ageppert/SAO_Etch_sAo_Sketch/Datasheets/OLED 1.5 128x128 drawing 2.png

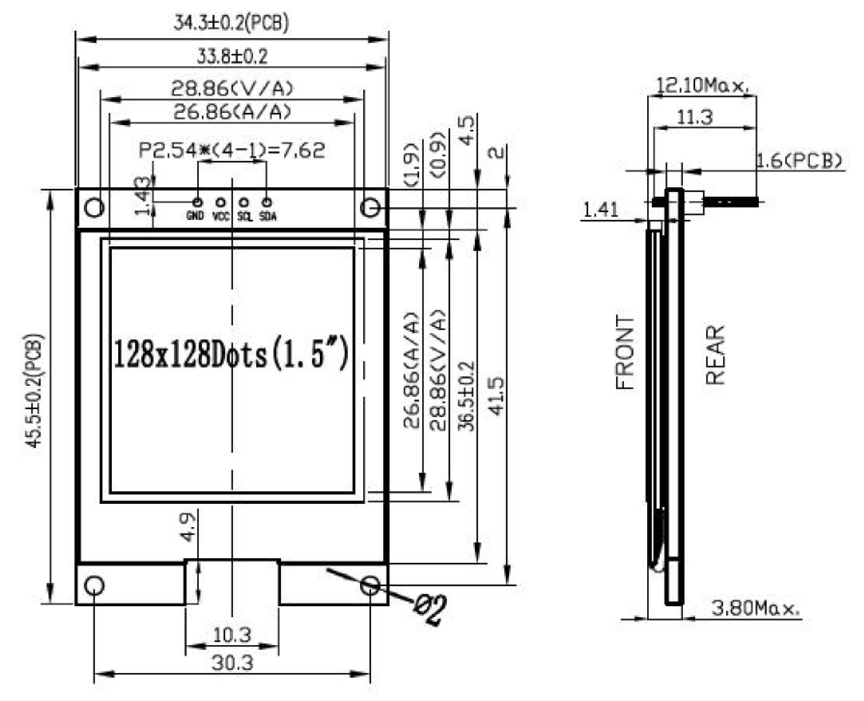
Datasheets/OLED 1.5 128x128 drawing 2.png
