ageppert/SAO_Etch_sAo_Sketch/Datasheets/OLED 1.5 GME128128-02 V3.1 with notch.png

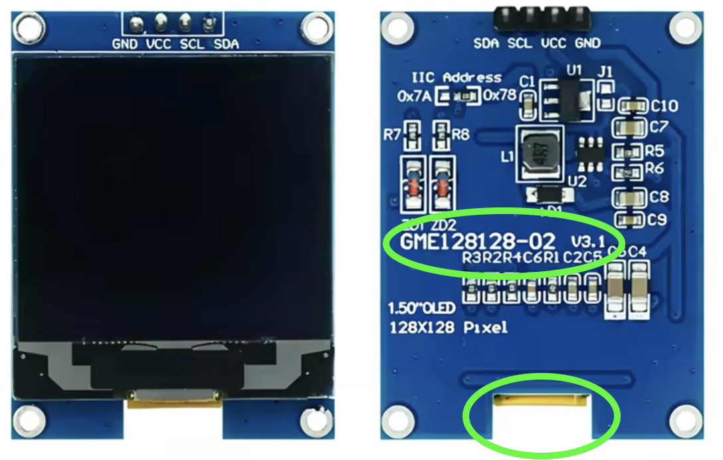
Datasheets/OLED 1.5 GME128128-02 V3.1 with notch.png
