ageppert/SAO_Etch_sAo_Sketch/Images/Etch_sAo_Sketch V1 Render Bottom.png

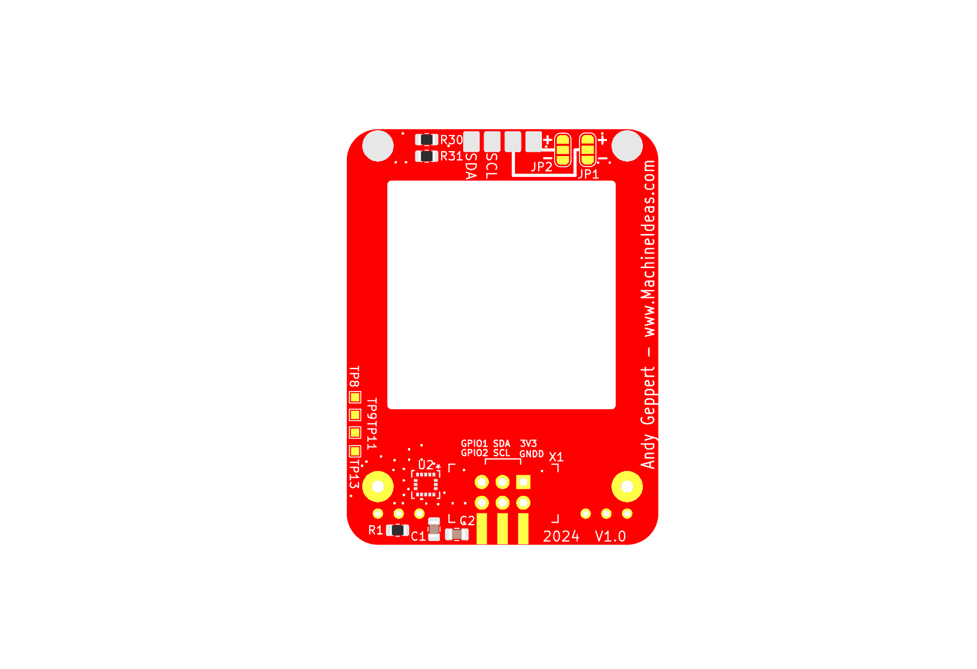
Images/Etch_sAo_Sketch V1 Render Bottom.png
