ageppert/SAO_Etch_sAo_Sketch/Images/GooDisplay 1.54.png

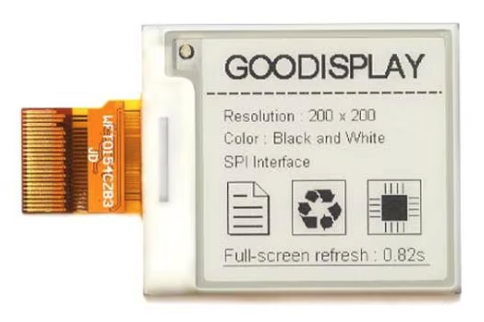
Images/GooDisplay 1.54.png
