ageppert/SAO_Etch_sAo_Sketch/Images/RIGHT OLED 128x128 V3 back side.jpg

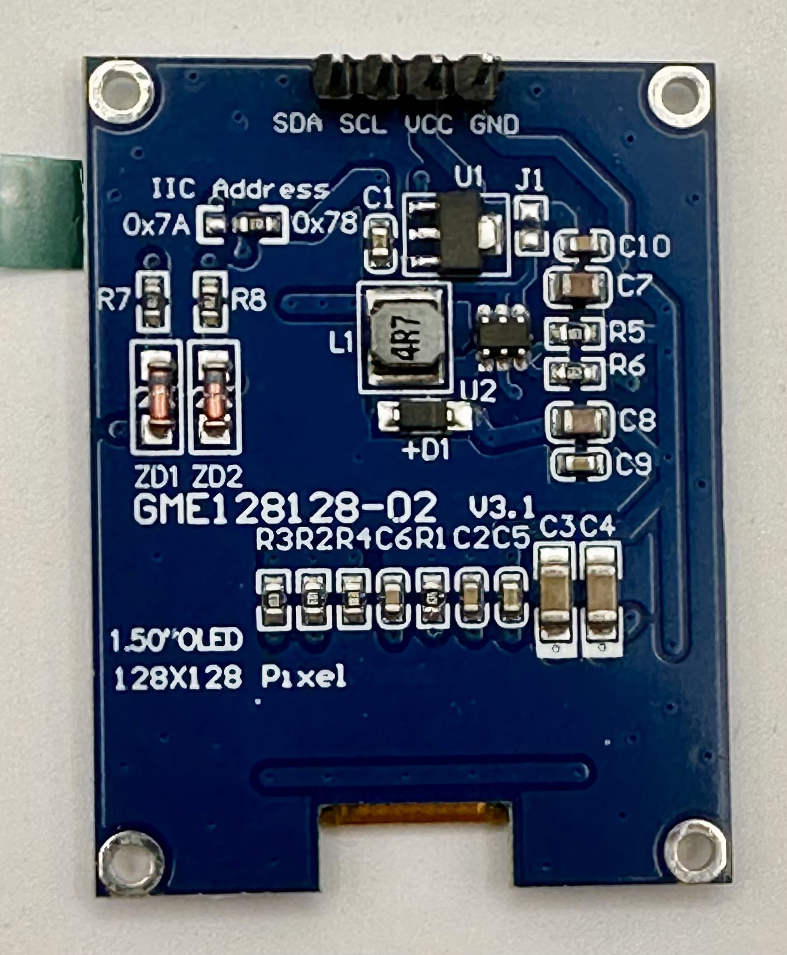
Images/RIGHT OLED 128x128 V3 back side.jpg
