ageppert/SAO_Etch_sAo_Sketch/Images/SAO Sketch Render Back V1.2.png

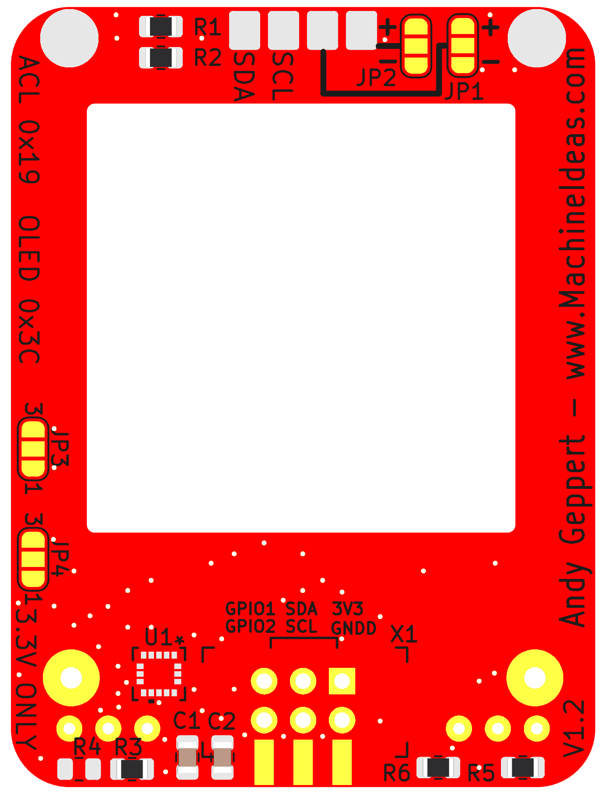
Images/SAO Sketch Render Back V1.2.png
