ageppert/SAO_Etch_sAo_Sketch/Images/SAO Sketch Render Front V1.3.png

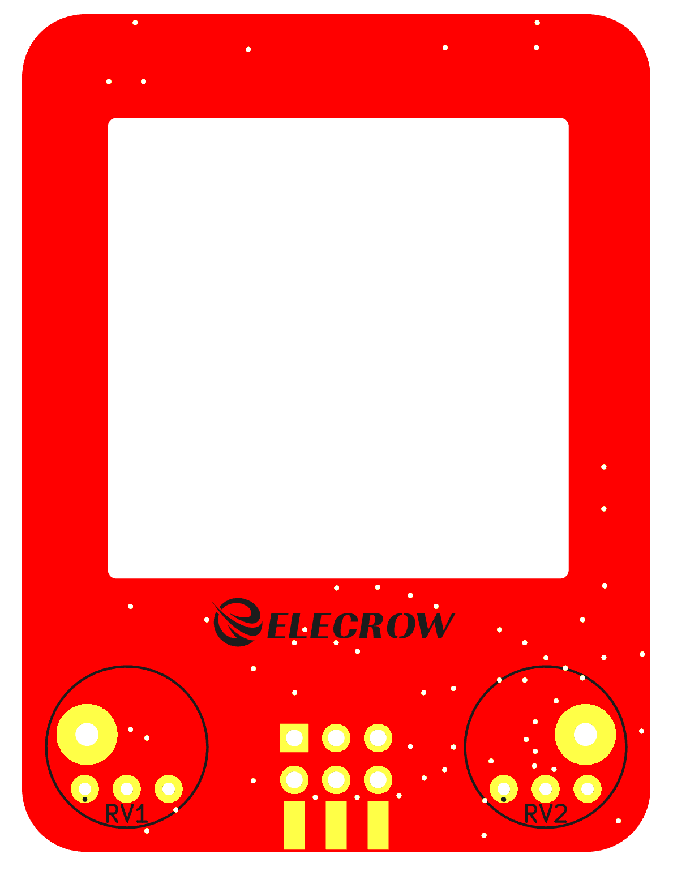
Images/SAO Sketch Render Front V1.3.png
