ageppert/SAO_Etch_sAo_Sketch/Images/Wrong OLED 128x128 V2.0 Advanced Tech.jpg

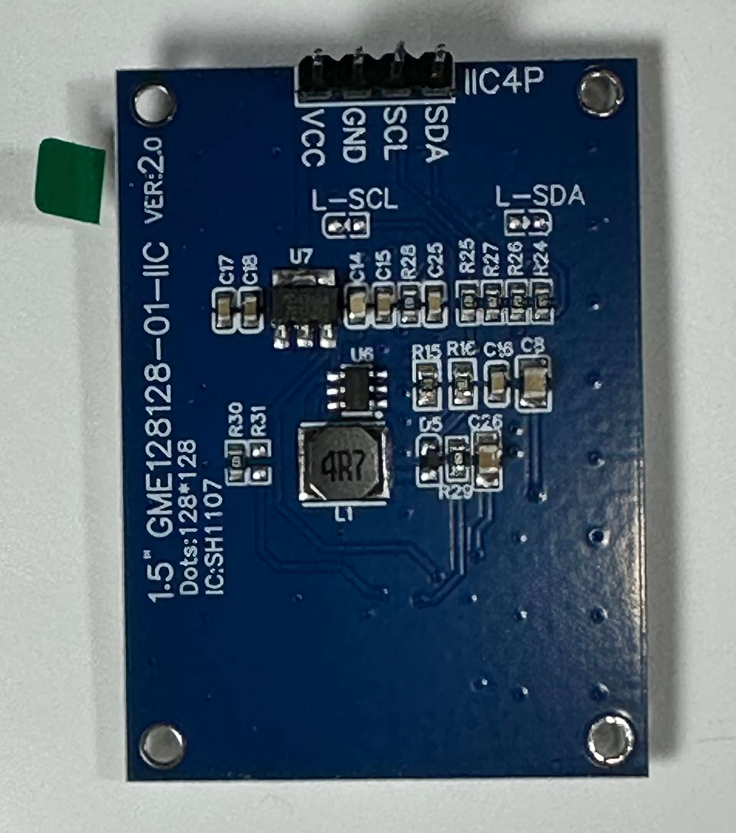
Images/Wrong OLED 128x128 V2.0 Advanced Tech.jpg
