ageppert/SAO_Etch_sAo_Sketch/Firmware/Supercon.8_Badge_Micropython/ssd1327.py

"""
MicroPython SSD1327 OLED I2C driver
https://github.com/mcauser/micropython-ssd1327

MIT License
Copyright (c) 2017 Mike Causer

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
__version__ = '1.1.1'

from micropython import const
import framebuf

# commands
SET_COL_ADDR          = const(0x15)
SET_SCROLL_DEACTIVATE = const(0x2E)
SET_ROW_ADDR          = const(0x75)
SET_CONTRAST          = const(0x81)
SET_SEG_REMAP         = const(0xA0)
SET_DISP_START_LINE   = const(0xA1)
SET_DISP_OFFSET       = const(0xA2)
SET_DISP_MODE         = const(0xA4) # 0xA4 normal, 0xA5 all on, 0xA6 all off, 0xA7 when inverted
SET_MUX_RATIO         = const(0xA8)
SET_FN_SELECT_A       = const(0xAB)
SET_DISP              = const(0xAE) # 0xAE power off, 0xAF power on
SET_PHASE_LEN         = const(0xB1)
SET_DISP_CLK_DIV      = const(0xB3)
SET_SECOND_PRECHARGE  = const(0xB6)
SET_GRAYSCALE_TABLE   = const(0xB8)
SET_GRAYSCALE_LINEAR  = const(0xB9)
SET_PRECHARGE         = const(0xBC)
SET_VCOM_DESEL        = const(0xBE)
SET_FN_SELECT_B       = const(0xD5)
SET_COMMAND_LOCK      = const(0xFD)

# registers
REG_CMD  = const(0x80)
REG_DATA = const(0x40)

class SSD1327:
    def __init__(self, width=128, height=128):
        self.width = width
        self.height = height
        self.buffer = bytearray(self.width * self.height // 2)
        self.framebuf = framebuf.FrameBuffer(self.buffer, self.width, self.height, framebuf.GS4_HMSB)

        self.col_addr = ((128 - self.width) // 4, 63 - ((128 - self.width) // 4))
        # 96x96     (8, 55)
        # 128x128   (0, 63)

        self.row_addr = (0, self.height - 1)
        # 96x96     (0, 95)
        # 128x128   (0, 127)

        self.offset = 128 - self.height
        # 96x96     32
        # 128x128   0

        self.poweron()
        self.init_display()

    def init_display(self):
        for cmd in (
            SET_COMMAND_LOCK, 0x12, # Unlock
            SET_DISP, # Display off
            # Resolution and layout
            SET_DISP_START_LINE, 0x00,
            SET_DISP_OFFSET, self.offset, # Set vertical offset by COM from 0~127
            # Set re-map
            # Enable column address re-map
            # Disable nibble re-map
            # Horizontal address increment
            # Enable COM re-map
            # Enable COM split odd even
            SET_SEG_REMAP, 0x51,
            SET_MUX_RATIO, self.height - 1,
            # Timing and driving scheme
            SET_FN_SELECT_A, 0x01, # Enable internal VDD regulator
            SET_PHASE_LEN, 0x51, # Phase 1: 1 DCLK, Phase 2: 5 DCLKs
            SET_DISP_CLK_DIV, 0x01, # Divide ratio: 1, Oscillator Frequency: 0
            SET_PRECHARGE, 0x08, # Set pre-charge voltage level: VCOMH
            SET_VCOM_DESEL, 0x07, # Set VCOMH COM deselect voltage level: 0.86*Vcc
            SET_SECOND_PRECHARGE, 0x01, # Second Pre-charge period: 1 DCLK
            SET_FN_SELECT_B, 0x62, # Enable enternal VSL, Enable second precharge
            # Display
            SET_GRAYSCALE_LINEAR, # Use linear greyscale lookup table
            SET_CONTRAST, 0x7f, # Medium brightness
            SET_DISP_MODE, # Normal, not inverted
            SET_COL_ADDR, self.col_addr[0], self.col_addr[1],
            SET_ROW_ADDR, self.row_addr[0], self.row_addr[1],
            SET_SCROLL_DEACTIVATE,
            SET_DISP | 0x01): # Display on
            self.write_cmd(cmd)
        self.fill(0)
        self.write_data(self.buffer)

    def poweroff(self):
        self.write_cmd(SET_FN_SELECT_A)
        self.write_cmd(0x00) # Disable internal VDD regulator, to save power
        self.write_cmd(SET_DISP)

    def poweron(self):
        self.write_cmd(SET_FN_SELECT_A)
        self.write_cmd(0x01) # Enable internal VDD regulator
        self.write_cmd(SET_DISP | 0x01)

    def contrast(self, contrast):
        self.write_cmd(SET_CONTRAST)
        self.write_cmd(contrast) # 0-255

    def rotate(self, rotate):
        self.poweroff()
        self.write_cmd(SET_DISP_OFFSET)
        self.write_cmd(self.height if rotate else self.offset)
        self.write_cmd(SET_SEG_REMAP)
        self.write_cmd(0x42 if rotate else 0x51)
        self.poweron()

    def invert(self, invert):
        self.write_cmd(SET_DISP_MODE | (invert & 1) << 1 | (invert & 1)) # 0xA4=Normal, 0xA7=Inverted

    def show(self):
        self.write_cmd(SET_COL_ADDR)
        self.write_cmd(self.col_addr[0])
        self.write_cmd(self.col_addr[1])
        self.write_cmd(SET_ROW_ADDR)
        self.write_cmd(self.row_addr[0])
        self.write_cmd(self.row_addr[1])
        self.write_data(self.buffer)

    def fill(self, col):
        self.framebuf.fill(col)

    def pixel(self, x, y, col):
        self.framebuf.pixel(x, y, col)

    def line(self, x1, y1, x2, y2, col):
        self.framebuf.line(x1, y1, x2, y2, col)

    def scroll(self, dx, dy):
        self.framebuf.scroll(dx, dy)
        # software scroll
        
    def text(self, string, x, y, col=15):
        self.framebuf.text(string, x, y, col)

    def write_cmd(self):
        raise NotImplementedError

    def write_data(self):
        raise NotImplementedError


class SSD1327_I2C(SSD1327):
    def __init__(self, width, height, i2c, addr=0x3c):
        self.i2c = i2c
        self.addr = addr
        self.cmd_arr = bytearray([REG_CMD, 0])  # Co=1, D/C#=0
        self.data_list = [bytes((REG_DATA,)), None]
        super().__init__(width, height)

    def write_cmd(self, cmd):
        self.cmd_arr[1] = cmd
        self.i2c.writeto(self.addr, self.cmd_arr)

    def write_data(self, data_buf):
        segments = self.split_into_segments(data_buf)
        for i, segment in enumerate(segments):
            self.data_list[1] = segment
            self.i2c.writevto(self.addr, self.data_list)

    def split_into_segments(self, ydata, segment_length=1024):
        """Split an array into segments, so we don't timeout"""
        return [ydata[i : i + segment_length] for i in range(0, len(ydata), segment_length)]


class WS_OLED_128X128(SSD1327_I2C):
    def __init__(self, i2c, addr=0x3c):
        super().__init__(128, 128, i2c, addr)
        
# Example usage
if __name__ == "__main__":
    from machine import Pin, SoftI2C
    # Initialize I2C
    i2c = SoftI2C(sda=Pin(26), scl=Pin(27))
    
    display = WS_OLED_128X128(i2c)

    display.fill(0)
    for x in range(0,127):
        for y in range(0,127):
            display.pixel(x,y,15)
            display.show()
    display.show()
