ageppert/SAO_Etch_sAo_Sketch/Firmware/Etch_sAo_Sketch_RP2040_Demo/Etch_sAo_Sketch_RP2040_Demo.ino

/******************************************************************************************************************
  Etch sAo Sketch (EAS) Demo code using RP2040 and the Arduino IDE

  Github repo: https://github.com/ageppert/SAO_Etch_sAo_Sketch
  Project page: https://hackaday.io/project/197581-etch-sao-sketch

  DEPENDENCIES - FIRMWARE
    This demo will work with a huge range of IDEs and hardware, but it was developed and tested with the following:
    Arduino IDE 2.3.2
      Install "Arduino Mbed OS RP2040 Boards" v4.2.2 with Arduino Boards Manager
        - The Wire Library is included.
      Adafruit SSD1327 libray with dependencies:
        - Adafruit BusIO
        - Adafruit GFX Library
      Adafruit LIS3DH libray with dependencies:
        - Adafruit BusIO
        - Adafruit Unified Sensor

  DEPENDENCIES - HARDWARE
    OLED with SSD1327 Driver
    Accelerometer LIS3DH
    External user provided RP2040 MCU tested so far

  CONFIGURE SAO DEMO CONTROLLER FOR ETCH SAO SKETCH HARDWARE V1.0
    If you are using SAO Demo Controller V2 with EAS V1.0 you need to close solder jumper JP5&6 pads 2-3 so the
    analog pots will be connected to GP26/ADC0 and GP27/ADC1 of the RP2040-Zero on the SAO Demo Controller. This enables
    access to the full range of the potentiometers in EAS V1.0 which are configured for 0 to 3.3V ADC sensing.
    Etch sAo Sketch V1.1+ can access full range pot control with the ADC in the accelerometer.

  CONFIGURE THIS FIRMWARE TO WORK WITH CORRECT ETCH SAO SKETCH HARDWARE
    See the ETCH SAO SKETCH - HARDWARE VERSION TABLE and hardware version setting variables immediately below it to compile
    this firmware to work correctly with your specific Etch sAo Sketch board.

  HARDWARE CONNECTIONS
    OLED 1.5" 128x128 SSD1327: https://learn.adafruit.com/adafruit-grayscale-1-5-128x128-oled-display/arduino-wiring-and-test
    Accelerometer LIS3DH: https://learn.sparkfun.com/tutorials/lis3dh-hookup-guide and https://learn.adafruit.com/adafruit-lis3dh-triple-axis-accelerometer-breakout/arduino  
    Demo board -> RP2040-Zero (miniature Pico/RP2040 dev board) https://www.waveshare.com/rp2040-zero.htm
    The SAO port (X1) is intended to provide full access to the accelerometer, screen, and analog pots.
    SAO I2C pins connect to the OLED and Accelerometer (which also has the potentionmeters connected to built-in ADCs).
    SAO GPIO1 pin connected to the left Analog Potentiometer
    SAO GPIO2 pin connected to the right Analog Potentiometer
  
  MODES OF OPERATION
    MODE_INIT
      Connect to the serial port for status and debugging  
    MODE_BOOT_SCREEN
      Startup with the boot screen. Configured analog input source per hardware version specified beloe the HARDWARE VERSION TABLE.
      After timeout, automatcally go to sketching mode with default black background.
    MODE_SKETCH
      In sketch mode, rotate pots to draw.
      Gestures active during sketch mode:
        Upsidedown, shake left/right to clear sketch zone.
        Rightsideup, shake left/right to change background color (also clears screen).
        Rightsideup, shake up/down to change pot input between Arduino Analog port (0-3.3V) or accelerometer analog ports (0.8-1.6V).
    MODE_AT_THE_END_OF_TIME
      I hope you never land in this mode!

  /************************************ ETCH SAO SKETCH - FWV (FIRMWARE VERSION) TABLE ******************************
  | VERSION |  DATE      | MCU     | DESCRIPTION                                                                    |
  -------------------------------------------------------------------------------------------------------------------
  |  1.0.0  | 2024-11-01 | RP2040  | First draft, hurry up for Supercon!
  |  1.1.0  | 2024-11-23 | RP2040  | Correct pot scaling for full range hardware mods with Accel ADC.
  |  1.3.0  | 2025-04-12 | RP2040  | Clarify hardware versions and configurations. Supports all hardware versions.
  |  1.3.1  | 2025-04-18 | RP2040  | Fix and improve shake side-to-side (upside down or right side up) to erase,
  |         |            |         |   disable screen inversion and pot input select gestures. Add LOAD and RUN, 
  |         |            |         |   and display firmware/hardware versions.
  |  1.3.2  | 2025-04-25 | RP2040  | Fix glitching wrap-around at ends by bounding ADC count reading with HWV1.3.
  |  1.3.3  | 2025-04-25 | RP2040  | Tighten ADC left/bottom range to ensure drawing to edges of screen with HWV1.1+.
  |  1.3.4  | 2025-08-16 | RP2040  | Quicker boot up, red LED breathing.
  |  1.3.5  | 2025-08-16 | RP2040  | Adjusted low end voltage/ADC to work with 3.0V supply, accounting for Demo Controller V2 diode drop.
  |  1.3.6  | 2025-09-26 | RP2040  | Add support to optionally connect Etch sAo Sketch to the incoming SAO port I2C1 to fully cover the Demo Controller.
  |  1.3.7  | 2026-09-05 | RP2040  | Add calibrate mode via GP14 Button (Demo Controller V2 button, and V3,V4 upper left USER BUTTON 1)
  |         |            |         |   Increase shake-to-clear sensitivity and enable up-down detection for clearing.
  |         |            |         |   Extend default Accelerometer ADC range to fit display better.
  |  1.4.0  | 2026-09-23 | RP2040  | Calibrate pot scaling for hardware version 1.4.0
  |         |            |         | 
  |         |            |         | 
  -----------------------------------------------------------------------------------------------------------------*/
  // TODO: Make this work with Hackaday Supercon 2024 and Berlin 2025 Badge I2C ports 4-5-6 on pins 31 CL / 32 DA GPIO 26/27. 
  //        Ports 1-2-3 on pins 1 DA and 2 CL. GPIO 0/1
    static uint8_t FirmwareVersionMajor  = 1;
    static uint8_t FirmwareVersionMinor  = 4;
    static uint8_t FirmwareVersionPatch  = 0;

  /************************************ ETCH SAO SKETCH - HWV (HARDWARE VERSION) TABLE ******************************
  | VERSION |  DATE      | ADC ?   | DESCRIPTION                                                                    |
  -------------------------------------------------------------------------------------------------------------------
  |  1.0.0  | 2024-09-27 | RP2040  | First prototype, as built, getting it to come alive. Analog input range of pots
  |         |            |  only   |   is much wider than accelerometer analog inputs can handle. Recommend to use
  |         |            |         |   only with 3.3V capable analog inputs of host MCU through SAO port GPIO1&2.
  |  1.0.1  | 2025-04-14 |         | First prototype, without excess pull-up resistors R30 and R31 10K.
  -------------------------------------------------------------------------------------------------------------------
  |  1.1.0  | 2024-11-23 | Accel   | V1.0.0 modified with resistors inline (10K highside and 4.8K lowside) with the
  |         |            |   or    |   pots to enable full travel to map to accelerometer ADC 0.8 to 1.6V input range.
  |  1.1.1  | 2025-04-25 | RP2040  | V1.1.0 with excess pull-up resistors R1/2 removed.
  -------------------------------------------------------------------------------------------------------------------
  |  1.2.0  | 2024-12-10 |         | RFQ only. Same as V1.1.0. Never produced.
  -------------------------------------------------------------------------------------------------------------------
  |  1.3.0  | 2025-01-13 | Accel   | Batch for Hackaday Europe with supplier name Elecrow on the front. Some may be
  |         |            |   or    |   updated with an additional clear Etch sAo Sketch sticker on the top as well.
  |  1.3.1  | 2025-04-13 | RP2040  | Removed R1 and R2 to reduce the excessive pull-up resistance for wider MCU
  |         |            |         |   compatibility (from the red board) and better I2C performance.
  |  1.3.2  | 2026-08-01 |         | Removed resistors R2 and R3 pull-ups and ZD1 and ZD2 diodes from the blue OLED
  |         |            |         |   Board for better I2C performance.
  -------------------------------------------------------------------------------------------------------------------
  |  1.4.0  | 2026-09-23 |         | Gold ENIG Etch sAo Sketch on top. Remove pull-up resistors on main board and 
  |         |            |         |   and OLED board. Remove OLED power solder jumpers.
  |         |            |         |
  -------------------------------------------------------------------------------------------------------------------
  ************************************* ETCH SAO SKETCH - HWV (HARDWARE VERSION) SETTING ****************************
  This will be the default mode of input from the analog pots (I2C Accelerometer ADC = 0 or Arduino/RP2040 ADCs = 1) 
  will be set during MODE_BOOT_SCREEN...                                                                           */
    static bool    EASAnalogSource;
  // ...based on the hardware version set in the following three lines.
    #define HARDWARE_VERSION_MAJOR  1
    #define HARDWARE_VERSION_MINOR  4
    #define HARDWARE_VERSION_PATCH  0
    static uint8_t HardwareVersionMajor  = HARDWARE_VERSION_MAJOR;
    static uint8_t HardwareVersionMinor  = HARDWARE_VERSION_MINOR;
    static uint8_t HardwareVersionPatch  = HARDWARE_VERSION_PATCH;
/*******************************************************************************************************************/

#include <Adafruit_SSD1327.h>
#include <Fonts/FreeMono9pt7b.h>  // https://learn.adafruit.com/adafruit-gfx-graphics-library/using-fonts
#include <Wire.h>                             // RP2040 Pico-Zero default I2C port is GPIO4 (SDA0) and GPIO5 (SCL0).
                                              // RP2040 Pico W default I2C port is GPIO4 (SDA0) and GPIO5 (SCL0).
#include <Adafruit_LIS3DH.h>
#include <Adafruit_Sensor.h>

/****** IMPORTANT ******
  Using the SAO Demo Controller's bottom SAO port with I2C1 means power will enter the system through the USB C port
  on the RP2040-zero. That power is regulated to 3.3V on the RP20240-Zero and must be routed to the I2C1 port. This requires:
    1) soldering on a small wire to the SAO Demo Controller from JP4 pin 1 to JP1 bottom pad 
    2) and removing D1.
  Of course, the SAO socket on the Demo Controller needs to be moved or installed on the top side of the board to accept the 
  Etch sAo Sketch on the top. For more details and illustrations, see the project page linked at the top of this file.
************************/
// Choose only one port by setting one of the following to true:
  // Default top SAO output port I2C0 channel
    #define I2C_PORT0 true
  // Optional use of the bottom SAO "input" port I2C1 channel as an output so Etch sAo Sketch and Demo Controller stack perfectly.
    #define I2C_PORT1 false

// Choose only one filter type
  #define EMA_FILTER     // Uses double precision floating point, slower compute
  // #define IIR_FILTER        // Uses integers, faster

// Filter strength 0 to 1, smaller numbers = heavier filtering
  #define EMA_FILTER_ALPHA_X 0.1
  #define EMA_FILTER_ALPHA_Y 0.1
  #define IIR_FILTER_ALPHA_X 0.05
  #define IIR_FILTER_ALPHA_Y 0.05

#define EAS_V1_4 true

#if I2C_PORT0
  #define I2C0_SDA_PIN 4
  #define I2C0_SCL_PIN 5
#endif

#if I2C_PORT1
  #define I2C1_SDA_PIN 2
  #define I2C1_SCL_PIN 3
#endif

#define UserButtonPin1 14
#define UserButtonPin2 15
#define UserButtonPin3  7
#define UserButtonPin4  6

#define LED_ENABLE
#ifdef LED_ENABLE
  #include <Adafruit_NeoPixel.h>
  #define PIN_RGB_LED 16
  #define NUMPIXELS 1
  Adafruit_NeoPixel pixels(NUMPIXELS, PIN_RGB_LED, NEO_RGB + NEO_KHZ800);
  #define LED_PEAK 4 // Highest brightness allowed (0-255)
  volatile uint32_t LEDNowTime = 0;
  volatile uint32_t LEDLastTime = 0;
  static uint32_t LEDDeltaTime = 100;
#endif

// #define DEBUG_SHAKE
// #define DEBUG_CURSOR
// #define DEBUG_ADC

#define OLED_ADDRESS                0x3C      // OLED SSD1327 is 0x3C
#define OLED_RESET                    -1
#define OLED_HEIGHT                  128
#define OLED_WIDTH                   128
#define OLED_WHITE                    15
#define OLED_GRAY                      7
#define OLED_BLACK                     0

#if I2C_PORT0
Adafruit_SSD1327 display(OLED_HEIGHT, OLED_WIDTH, &Wire, OLED_RESET, 400000);
#endif
#if I2C_PORT1
Adafruit_SSD1327 display(OLED_HEIGHT, OLED_WIDTH, &Wire1, OLED_RESET, 400000);
#endif

static uint8_t  color = OLED_WHITE;                        // 0-15 shades of gray
static uint16_t cursorX = 0;                               // 0-127 pixels
static uint16_t cursorY = 0;                               // 0-127 pixels
static uint16_t cursorXold = 0;                            // 0-127 pixels
static uint16_t cursorYold = 0;                            // 0-127 pixels
static bool     EASBackground = 0;                         // 0 = dark (default), 1 = white (display doesn't look as good)
static uint8_t  CursorPosXLeft = 13;
static uint8_t  CursorPosX = CursorPosXLeft;
static uint8_t  CursorPosY = 0;
static uint8_t  CursorHeight = 7;
static uint8_t  CursorWidth =  6;
static uint8_t  CursorNewLine = 8;
static bool     CursorState = 0;
static uint32_t NowTime;
static uint32_t LastTime;
static uint32_t BlinkDeltaTime = 600;
static uint8_t KeyStrokeDelay = 25; // 0-255 ms

#define ACCELEROMETER_ADDRESS       0x19      // LIS3DH Acceleromter default is 0x19
#if I2C_PORT0
  Adafruit_LIS3DH lis = Adafruit_LIS3DH();
#endif
#if I2C_PORT1
  Adafruit_LIS3DH lis = Adafruit_LIS3DH(&Wire1);
#endif

#define PIN_SAO_GPIO_1_ANA_POT_LEFT   A0      // Configured as left analog pot
#define PIN_SAO_GPIO_2_ANA_POT_RIGHT  A1      // Configured as right analog pot
#define PIN_ANA_CURRENT_MON           A2
#define PIN_ANA_VOLTAGE_MON           A3
uint16_t PotLeftADCCounts = 0;
uint16_t PotRightADCCounts = 0;
uint16_t PotLeftADCCountsOld = 0;
uint16_t PotRightADCCountsOld = 0;
uint16_t PotMarginAtLimit = 10;
// uint16_t PotHystersisLimit = 12;
// uint16_t PotGlitchLimit = 64;
// uint16_t PotFilterSampleCount = 3;
// uint16_t deltaAbsolute = 0;
// uint16_t CursorHystersisLimit = 4;

#if (HARDWARE_VERSION_MAJOR  == 1) && (HARDWARE_VERSION_MINOR  == 4)
  int16_t AccelADCRangeLowCounts  = -6500; // 9000 works better with 3V supply. Was -1500;      // Tested with 3.3V supply voltage, R5 10K, R6 4K7
  int16_t AccelADCRangeHighCounts = 26000;
  int16_t AccelADCRangeLowmV      =   900;
  int16_t AccelADCRangeHighmV;
#else
  int16_t AccelADCRangeLowCounts  = -3200; // 9000 works better with 3V supply. Was -1500;      // Tested with 3.3V supply voltage, R5 10K, R6 4K7
  int16_t AccelADCRangeHighCounts = 30000;
  int16_t AccelADCRangeLowmV      =   900;
  int16_t AccelADCRangeHighmV;
#endif 

enum TopLevelMode                             // Top Level Mode State Machine
{
  MODE_INIT,
  MODE_BOOT_SCREEN,
  MODE_LOAD,
  MODE_LOADING,
  MODE_RUN,
  MODE_SKETCH,
  MODE_CALIBRATE,
  MODE_AT_THE_END_OF_TIME
} ;
uint8_t  TopLevelMode = MODE_INIT;
uint8_t  TopLevelModeDefault = MODE_BOOT_SCREEN;
uint32_t ModeTimeoutDeltams = 0;
uint32_t ModeTimeoutFirstTimeRun = true;

class EmaFilterWithPriming
// from https://blog.mbedded.ninja/programming/signal-processing/digital-filters/exponential-moving-average-ema-filter
// with minimal round-off error, noticeable lag with the double precision calcs
// Alpha (0 to 1) is cut-off frequency, lower number is more filtering
{
  public:
      EmaFilterWithPriming(double alpha) :
          m_alpha(alpha), m_lastOutput(0.0), m_firstRun(true) {}

      double Run(double input)
      {
          if (m_firstRun)
          {
              m_firstRun = false;
              m_lastOutput = input; // Bypass filter and prime with input
          }
          else
          {
              m_lastOutput = m_alpha * input + (1 - m_alpha) * m_lastOutput;
          }
          return m_lastOutput;
      }
  private:
      double m_alpha;
      double m_lastOutput;
      bool m_firstRun;
  };
  EmaFilterWithPriming emaFilterX(EMA_FILTER_ALPHA_X);
  EmaFilterWithPriming emaFilterY(EMA_FILTER_ALPHA_Y);

  // TODO: IMPLEMENT THE BIT SHIFT IIR THAT WORKS TO THE POLES
  class IIRFilterWithIntegers
  // from https://electronics.stackexchange.com/questions/30370/fast-and-memory-efficient-moving-average-calculation
  // and https://forum.arduino.cc/t/understanding-some-code/499217 
  // with round-off error, but very fast with bit shifting
  // where alpha = 1 / 2^BITFILTER
  {
  public:
      IIRFilterWithIntegers(double alpha) :
          m_alpha(alpha), m_lastOutput(0.0), m_firstRun(true) {}

      double Run(double input)
      {
          if (m_firstRun)
          {
              m_firstRun = false;
              m_lastOutput = input; // Bypass filter and prime with input
          }
          else
          {
              m_lastOutput = m_alpha * input + (1 - m_alpha) * m_lastOutput;
          }
          return m_lastOutput;
      }
  private:
      double m_alpha;
      double m_lastOutput;
      bool m_firstRun;
};

IIRFilterWithIntegers IIRFilterX(IIR_FILTER_ALPHA_X);
IIRFilterWithIntegers IIRFilterY(IIR_FILTER_ALPHA_Y);

void setup()
{
  #if I2C_PORT0
    // Set the SDA and SCL pins for the Wire1 object before beginning
    Wire.setSDA(I2C0_SDA_PIN);
    Wire.setSCL(I2C0_SCL_PIN);
    Wire.begin();
    Wire.setClock(400000); 
  #endif

  #if I2C_PORT1
    // Set the SDA and SCL pins for the Wire1 object before beginning
    Wire1.setSDA(I2C1_SDA_PIN);
    Wire1.setSCL(I2C1_SCL_PIN);
    Wire1.begin();
    Wire1.setClock(400000); 
  #endif
}

bool SerialInit() {
  bool StatusSerial = 1;
  Serial.begin(115200);
  // TODO get rid of this delay, quickly detect presence of serial port, and send message only if it's detected.
  delay(1500);
  Serial.println("\nHello World! This is the serial port talking!");
  return StatusSerial;
}

bool OLEDInit() {
  Serial.print(">>> INIT OLED started... ");
  if ( ! display.begin(OLED_ADDRESS) ) {
     Serial.println("Unable to initialize OLED");
     return 1;
  }
  else {
    Wire.setClock(400000); 
    Serial.println("Initialized!");
    OLEDClear();
  }
  return 0;
}

bool LEDInit() {
  #ifdef LED_ENABLE
    pixels.begin();
    return 0;
  #endif
  return 1;
}

void LEDBreath() {
  #ifdef LED_ENABLE
    static uint8_t brightness = 0;
    static bool increasing = true;

    // Is it time to change brightness?
    LEDNowTime = millis();
    if ( (LEDNowTime-LEDLastTime) > LEDDeltaTime) {
      LEDLastTime = LEDNowTime;
      if (increasing) {
        if (brightness < LED_PEAK) {
          brightness++;
        }
        else {
          increasing = false;
        }
      }
      else {
        if (brightness > 0) {
          brightness--;
        }
        else {
          increasing = true;
        }
      }
      pixels.setPixelColor(0, pixels.Color(0, brightness, 0));
      pixels.show();
    }
  #endif
}

bool AccelerometerInit() {
  Serial.print(">>> INIT Accelerometer LIS3DH started... ");
  if (! lis.begin(ACCELEROMETER_ADDRESS)) {   // change this to 0x19 for alternative i2c address
    Serial.println("Unable to initialize.");
    return 1;
  }
  else {
    Wire.setClock(400000); 
    Serial.println("Initialized!");
    AccelerometerQuerySettings();
  }
  return 0;
}

void AccelerometerQuerySettings() {
  Serial.println("    Accelerometer LIS3DH Settings:");  
  Serial.print("    Range = "); Serial.print(2 << lis.getRange());
  Serial.println("G");

  // lis.setPerformanceMode(LIS3DH_MODE_LOW_POWER);
  Serial.print("    Performance mode set to: ");
  switch (lis.getPerformanceMode()) {
    case LIS3DH_MODE_NORMAL: Serial.println("Normal 10bit"); break;
    case LIS3DH_MODE_LOW_POWER: Serial.println("Low Power 8bit"); break;
    case LIS3DH_MODE_HIGH_RESOLUTION: Serial.println("High Resolution 12bit"); break;
  }

  // lis.setDataRate(LIS3DH_DATARATE_50_HZ);
  Serial.print("    Data rate set to: ");
  switch (lis.getDataRate()) {
    case LIS3DH_DATARATE_1_HZ: Serial.println("1 Hz"); break;
    case LIS3DH_DATARATE_10_HZ: Serial.println("10 Hz"); break;
    case LIS3DH_DATARATE_25_HZ: Serial.println("25 Hz"); break;
    case LIS3DH_DATARATE_50_HZ: Serial.println("50 Hz"); break;
    case LIS3DH_DATARATE_100_HZ: Serial.println("100 Hz"); break;
    case LIS3DH_DATARATE_200_HZ: Serial.println("200 Hz"); break;
    case LIS3DH_DATARATE_400_HZ: Serial.println("400 Hz"); break;

    case LIS3DH_DATARATE_POWERDOWN: Serial.println("Powered Down"); break;
    case LIS3DH_DATARATE_LOWPOWER_5KHZ: Serial.println("5 Khz Low Power"); break;
    case LIS3DH_DATARATE_LOWPOWER_1K6HZ: Serial.println("1.6 Khz Low Power"); break;
  }  
}

void AccelerometerReadAccel() {
  lis.read();      // get X Y and Z data at once
  // Then print out the raw data
  // Serial.print("X:  "); Serial.print(lis.x);
  // Serial.print("  \tY:  "); Serial.print(lis.y);
  // Serial.print("  \tZ:  "); Serial.print(lis.z);

  /* Or....get a new sensor event, normalized */
  // sensors_event_t event;
  // lis.getEvent(&event);

  /* Display the results (acceleration is measured in m/s^2) */
  // Serial.print("\t\tX: "); Serial.print(event.acceleration.x);
  // Serial.print(" \tY: "); Serial.print(event.acceleration.y);
  // Serial.print(" \tZ: "); Serial.print(event.acceleration.z);
  // Serial.println(" m/s^2 ");

  // Serial.println();
}

bool AccelerometerSenseGestureErase() {
  bool UpSideDown;
  bool ShakeUp;
  bool ShakeDown;
  bool ShakeLeft;
  bool ShakeRight;
  bool ShakeInProgress;
  static uint16_t ShakeUpCount;
  static uint16_t ShakeDownCount;
  static uint16_t ShakeLeftCount;
  static uint16_t ShakeRightCount;
  static uint16_t ShakeSensitivyThreshold = 8000;
  static uint16_t ShakeCountThreshold = 50;
  static uint32_t ShakeTimeout = 1000; // Window of time that shaking must be active to clear the screen
  static uint32_t ShakeTimeNow;
  static uint32_t ShakeTimeLast = 0;
  ShakeTimeNow = millis();
  AccelerometerReadAccel();
  // Is it up-side-down?
  // if (lis.z > 10000) { UpSideDown = true;  }
  // else               { UpSideDown = false; }
  // Check for Left shake
  if (lis.y > ShakeSensitivyThreshold) { ShakeLeft = true; ShakeTimeLast = ShakeTimeNow; }
  else               { ShakeLeft = false; }
  // Check for Right shake
  if (lis.y < -ShakeSensitivyThreshold) { ShakeRight = true; ShakeTimeLast = ShakeTimeNow; }
  else                { ShakeRight = false; }
  // Check for Up shake
  if (lis.x > ShakeSensitivyThreshold) { ShakeUp = true; ShakeTimeLast = ShakeTimeNow; }
  else               { ShakeUp = false; }
  // Check for Down shake
  if (lis.x < -ShakeSensitivyThreshold) { ShakeDown = true; ShakeTimeLast = ShakeTimeNow; }
  else                { ShakeDown = false; }

  if ((ShakeTimeNow - ShakeTimeLast) < ShakeTimeout) {ShakeInProgress = true;}
  else {ShakeInProgress = false;}
  // If it is actively being shaken...
  if (ShakeInProgress) {
    // ...Accumulate left/right and up/down shakes...
    if (ShakeLeft) { ShakeLeftCount++; }
    if (ShakeRight) { ShakeRightCount++; }
    if (ShakeUp) { ShakeUpCount++; }
    if (ShakeDown) { ShakeDownCount++; }
  }
  // ...otherwise reset the counters.
  else {
    ShakeLeftCount = 0;
    ShakeRightCount = 0;
    ShakeUpCount = 0;
    ShakeDownCount = 0;
  }
  #ifdef DEBUG_SHAKE
    Serial.print(ShakeLeftCount);
    Serial.print(", ");
    Serial.print(ShakeRightCount);
    Serial.print(", ");
    Serial.print(ShakeUpCount);
    Serial.print(", ");
    Serial.println(ShakeDownCount);
  #endif
  // If all conditions are met, signal screen clearing.
  if ( (ShakeLeftCount > ShakeCountThreshold) && (ShakeRightCount > ShakeCountThreshold) ||
       (ShakeUpCount > ShakeCountThreshold) && (ShakeDownCount > ShakeCountThreshold)       ) {
    ShakeLeftCount = 0;
    ShakeRightCount = 0;
    ShakeUpCount = 0;
    ShakeDownCount = 0;
    OLEDBackgroundReset();
    return 1;
  }
  else { return 0; }
}

bool AccelerometerSenseGestureChangeBackground() {
  bool RightSideUp;
  bool ShakeLeft;
  bool ShakeRight;
  static uint16_t ShakeLeftCount;
  static uint16_t ShakeRightCount;
  static uint16_t ShakeSensitivyThreshold = 7000;
  static uint16_t ShakeCountThreshold = 20;
  AccelerometerReadAccel();
  // Is it up-side-down?
  if (lis.z < 10000) { RightSideUp = true;  }
  else               { RightSideUp = false; }
  // Check for Left shake
  if (lis.y > ShakeSensitivyThreshold) { ShakeLeft = true;  }
  else               { ShakeLeft = false; }
  // Check for Right shake
  if (lis.y < -ShakeSensitivyThreshold) { ShakeRight = true;  }
  else                { ShakeRight = false; }
  // If it is right-side-up...
  if (RightSideUp) {
    // ...Accumulate left/right shakes...
    if (ShakeLeft) { ShakeLeftCount++; }
    if (ShakeRight) { ShakeRightCount++; }
  }
  // ...otherwise reset the counters.
  else {
    ShakeLeftCount = 0;
    ShakeRightCount = 0;
  }
  // If all conditions are met, signal background color change.
  if ((ShakeLeftCount > ShakeCountThreshold) && (ShakeRightCount > ShakeCountThreshold)) {
    ShakeLeftCount = 0;
    ShakeRightCount = 0;
    return 1;
  }
  else { return 0; }
}

bool AccelerometerSenseGestureChangeADCSource() {
  bool RightSideUp;
  bool ShakeUp;
  bool ShakeDown;
  static uint16_t ShakeUpCount;
  static uint16_t ShakeDownCount;
  static uint16_t ShakeSensitivyThreshold = 8000;
  static uint16_t ShakeCountThreshold = 30;
  AccelerometerReadAccel();
  // Is it up-side-down?
  if (lis.z < 10000) { RightSideUp = true;  }
  else               { RightSideUp = false; }
  // Check for up shake
  if (lis.x > ShakeSensitivyThreshold) { ShakeUp = true;  }
  else               { ShakeUp = false; }
  // Check for down shake
  if (lis.x < -ShakeSensitivyThreshold) { ShakeDown = true;  }
  else                { ShakeDown = false; }
  // If it is right-side-up...
  if (RightSideUp) {
    // ...Accumulate up/down shakes...
    if (ShakeUp) { ShakeUpCount++; }
    if (ShakeDown) { ShakeDownCount++; }
  }
  // ...otherwise reset the counters.
  else {
    ShakeUpCount = 0;
    ShakeDownCount = 0;
  }
  // If all conditions are met, signal ADC source change.
  if ((ShakeUpCount > ShakeCountThreshold) && (ShakeDownCount > ShakeCountThreshold)) {
    ShakeUpCount = 0;
    ShakeDownCount = 0;
    return 1;
  }
  else { return 0; }
}

void OLEDClear() {
  display.clearDisplay();
  display.display();
}

void OLEDFill() {
  display.fillRect(0,0,display.width(),display.height(),OLED_WHITE);
  display.display();
}

void OLEDBackgroundReset() {
  if (EASBackground) { OLEDFill();  }
  else               { OLEDClear(); }
}

void SAOGPIOPinInit (){
  pinMode(UserButtonPin1, INPUT_PULLUP);
  pinMode(UserButtonPin2, INPUT_PULLUP);
  pinMode(UserButtonPin3, INPUT_PULLUP);
  pinMode(UserButtonPin4, INPUT_PULLUP);
  // Nothing else to do because analog input is default for Arduino.
}

void SAOAnalogInit () {
  #if I2C_PORT0
    AccelADCRangeHighmV     =  1200; // 1200 works better with 3V supply.
  #endif
  #if I2C_PORT1
    AccelADCRangeHighmV     =  1400; // 1400 works better with 3.3V supply.
  #endif

}

void ModeTimeOutCheckReset () {
  ModeTimeoutDeltams = 0;
  ModeTimeoutFirstTimeRun = true;
}

bool ModeTimeOutCheck (uint32_t ModeTimeoutLimitms) {
  static uint32_t NowTimems;
  static uint32_t StartTimems;
  NowTimems = millis();
  if(ModeTimeoutFirstTimeRun) { StartTimems = NowTimems; ModeTimeoutFirstTimeRun = false;}
  ModeTimeoutDeltams = NowTimems-StartTimems;
  if (ModeTimeoutDeltams >= ModeTimeoutLimitms) {
    ModeTimeOutCheckReset();
    Serial.print(">>> Mode timeout after ");
    Serial.print(ModeTimeoutLimitms);
    Serial.println(" ms.");
    return (true);
  }
  else {
    return (false);
  }
}

void CursorBlink() {
  // Is it time to blink?
  NowTime = millis();
  if ( (NowTime-LastTime) > BlinkDeltaTime) {
    // Blink the cursor
    LastTime = NowTime;
    if (CursorState) { display.fillRect(CursorPosX,CursorPosY,CursorWidth,CursorHeight,SSD1327_WHITE); CursorState = 0;}
    else { display.fillRect(CursorPosX,CursorPosY,CursorWidth,CursorHeight,SSD1327_BLACK);  CursorState = 1;}
    display.display();
  }
}

void CursorErase() {
  display.fillRect(CursorPosX,CursorPosY,CursorWidth,CursorHeight,SSD1327_BLACK);
  CursorState = 1;
  display.display();
}

void  PowerMonitor() {

  uint16_t AdcRawUnmapped;
  uint16_t AdcRawBBVoltage;
  uint16_t AdcRawOutCurrent;
  uint16_t AdcRawBatVoltage;

  // uint16_t AdcRawUnmapped;
  uint16_t AdcBBVoltagemV;
  uint16_t AdcOutCurrentmA;
  uint16_t AdcBatVoltagemV;

  AdcRawUnmapped = analogRead(PIN_SAO_GPIO_1_ANA_POT_LEFT);

  AdcRawBBVoltage = analogRead(PIN_SAO_GPIO_2_ANA_POT_RIGHT);
  AdcBBVoltagemV = (AdcRawBBVoltage * 3300 / 1023 * 1.06 );

  AdcRawOutCurrent = analogRead(PIN_ANA_CURRENT_MON);
  AdcOutCurrentmA = (AdcRawOutCurrent * 3300 / 1023 / 2.5 );

  AdcRawBatVoltage = analogRead(PIN_ANA_VOLTAGE_MON);
  AdcBatVoltagemV = (AdcRawBatVoltage * 3300 / 1023 * 4.73 );

  Serial.print("A0_unmapped: ");
  Serial.print(AdcRawUnmapped);
  Serial.print("     ");
  Serial.print("A1_SAO Buck-Boost(mV): ");
  Serial.print(AdcBBVoltagemV);
  Serial.print("     ");
  Serial.print("A2_SAO Load Current(mA): ");
  Serial.print(AdcOutCurrentmA);
  Serial.print("     ");
  Serial.print("A3_VIN_VSW(mV): ");
  Serial.println(AdcBatVoltagemV);

}


// -------------------------------------------------------------------------------------------
// MAIN LOOP STARTS HERE
// -------------------------------------------------------------------------------------------
void loop()
{
  #ifdef LED_ENABLE
    LEDBreath();
  #endif

  // PowerMonitor();

  switch(TopLevelMode) {
    case MODE_INIT: {
      SerialInit();
      Serial.println(">>> Entered MODE_INIT.");
      OLEDInit();
      #ifdef LED_ENABLE
        LEDInit();
      #endif
      AccelerometerInit();
      SAOGPIOPinInit();
      SAOAnalogInit();
      Serial.println("");
      Serial.println("  |------------------------------------------------------------------------------------| ");
      Serial.println("  | Welcome to the Etch sAo Sketch Demo made with Arduino IDE 2.3.2 using RP2040-Zero! | ");
      Serial.println("  |------------------------------------------------------------------------------------| ");
      Serial.println("");
      Serial.print("Hardware Version: ");
      Serial.print(HardwareVersionMajor);
      Serial.print(".");
      Serial.print(HardwareVersionMinor );
      Serial.print(".");
      Serial.println(HardwareVersionPatch);
      Serial.print("Firmware Version: ");
      Serial.print(FirmwareVersionMajor);
      Serial.print(".");
      Serial.print(FirmwareVersionMinor );
      Serial.print(".");
      Serial.println(FirmwareVersionPatch);
      ModeTimeOutCheckReset(); 
      TopLevelMode = TopLevelModeDefault;
      Serial.println(">>> Leaving MODE_INIT.");
      break;
    }

    case MODE_BOOT_SCREEN: {
      if (ModeTimeoutFirstTimeRun) {
        ModeTimeoutFirstTimeRun = false;
        Serial.println(">>> Entered MODE_BOOT_SCREEN.");
        OLEDClear();
        display.display();
        // Border
        uint8_t BorderThickness = 11;
        for (uint8_t i=0; i<BorderThickness; i+=1) {
          display.drawRect(i, i, display.width()-2*i, display.height()-2*i, OLED_WHITE);
        }
        display.display();
        delay(500);
        // Background
        // display.fillRect(2*BorderThickness,BorderThickness,2*BorderThickness,2*BorderThickness,OLED_GRAY);
        //for (uint8_t i=BorderThickness; i<display.height(); i+=1) {
        //  display.drawRect(i, i, display.width()-2*i-BorderThickness, display.height()-2*i-BorderThickness, OLED_GRAY);
        //}
        // display.setFont(&FreeMono9pt7b);
        display.setTextSize(1);
        // display.cp437(true);
        display.setTextColor(SSD1327_WHITE);
        CursorPosX = CursorPosXLeft;
        CursorPosY = CursorPosY + CursorNewLine + CursorNewLine;
        display.setCursor(CursorPosX,CursorPosY);
        display.print(" ETCH sAo SKETCH");
        display.display();
        CursorPosX = CursorPosXLeft;
        CursorPosY = CursorPosY + CursorNewLine;
        display.setCursor(CursorPosX,CursorPosY);
        display.print("    HWV ");
        display.print(HardwareVersionMajor);
        display.print(".");
        display.print(HardwareVersionMinor);
        display.print(".");
        display.print(HardwareVersionPatch);
        display.display();
        CursorPosX = CursorPosXLeft;
        CursorPosY = CursorPosY + CursorNewLine;
        display.setCursor(CursorPosX,CursorPosY);
        display.print("  64 BYTES FREE");
        display.display();
        CursorPosX = CursorPosXLeft;
        CursorPosY = CursorPosY + CursorNewLine + CursorNewLine;
        display.setCursor(CursorPosX,CursorPosY);
        display.print("READY.");
        display.display();
        CursorPosX = CursorPosXLeft;
        CursorPosY = CursorPosY + CursorNewLine;
        display.setCursor(CursorPosX,CursorPosY);
        // Configure analog input source based on hardware version.
        // See comments at top of this file in ETCH SAO SKETCH - HARDWARE VERSION TABLE for expected input source
        // 0 = accelerometer ADC, 1 = Arduino Analog Ports
        if (HardwareVersionMajor == 1) {
          if      (HardwareVersionMinor == 0) { EASAnalogSource = 1; }
          else if (HardwareVersionMinor == 1) { EASAnalogSource = 0; }
          else if (HardwareVersionMinor == 2) { EASAnalogSource = 0; }
          else if (HardwareVersionMinor == 3) { EASAnalogSource = 0; }
        }
        ModeTimeOutCheckReset();
      }
      CursorBlink();
      if (ModeTimeOutCheck(1500)){ 
        ModeTimeOutCheckReset();
        CursorErase();
        TopLevelMode++;
        ModeTimeoutFirstTimeRun = true;
        Serial.println(">>> Leaving MODE_BOOT_SCREEN.");
      }
      break;
    }

    case MODE_LOAD: {
      if (ModeTimeoutFirstTimeRun) {
        ModeTimeoutFirstTimeRun = false;
        Serial.println(">>> Entered MODE_LOAD.");
        display.println("L");
        display.display();
        delay(KeyStrokeDelay);
        CursorPosX = CursorPosX + 6;
        display.setCursor(CursorPosX,CursorPosY);
        display.println("O");
        display.display();
        delay(KeyStrokeDelay);
        CursorPosX = CursorPosX + 6;
        display.setCursor(CursorPosX,CursorPosY);
        display.println("A");
        display.display();
        delay(KeyStrokeDelay);
        CursorPosX = CursorPosX + 6;
        display.setCursor(CursorPosX,CursorPosY);
        display.println("D");
        display.display();
        delay(KeyStrokeDelay);
        ModeTimeOutCheckReset();
        CursorPosX = CursorPosX + 6;
        display.setCursor(CursorPosX,CursorPosY);
        display.println("\"");
        display.display();
        delay(KeyStrokeDelay);
        ModeTimeOutCheckReset();
        CursorPosX = CursorPosX + 6;
        display.setCursor(CursorPosX,CursorPosY);
        display.println("S");
        display.display();
        delay(KeyStrokeDelay);
        ModeTimeOutCheckReset();
        CursorPosX = CursorPosX + 6;
        display.setCursor(CursorPosX,CursorPosY);
        display.println("K");
        display.display();
        delay(KeyStrokeDelay);
        ModeTimeOutCheckReset();
        CursorPosX = CursorPosX + 6;
        display.setCursor(CursorPosX,CursorPosY);
        display.println("E");
        display.display();
        delay(KeyStrokeDelay);
        ModeTimeOutCheckReset();
        CursorPosX = CursorPosX + 6;
        display.setCursor(CursorPosX,CursorPosY);
        display.println("T");
        display.display();
        delay(KeyStrokeDelay);
        ModeTimeOutCheckReset();
        CursorPosX = CursorPosX + 6;
        display.setCursor(CursorPosX,CursorPosY);
        display.println("C");
        display.display();
        delay(KeyStrokeDelay);
        ModeTimeOutCheckReset();
        CursorPosX = CursorPosX + 6;
        display.setCursor(CursorPosX,CursorPosY);
        display.println("H");
        display.display();
        delay(KeyStrokeDelay);
        ModeTimeOutCheckReset();
        CursorPosX = CursorPosX + 6;
        display.setCursor(CursorPosX,CursorPosY);
        display.println("\"");
        display.display();
        delay(KeyStrokeDelay);
        ModeTimeOutCheckReset();
        CursorPosX = CursorPosX + 6;
      }
      CursorBlink();
      if (ModeTimeOutCheck(500)){ 
        ModeTimeOutCheckReset();
        CursorErase();
        TopLevelMode++;
        ModeTimeoutFirstTimeRun = true;
        Serial.println(">>> Leaving MODE_LOAD.");
      }
      break;
    }

    case MODE_LOADING: {
      if (ModeTimeoutFirstTimeRun) { 
        ModeTimeoutFirstTimeRun = false;
        Serial.println(">>> Entered MODE_LOADING.");
        CursorPosX = CursorPosXLeft;
        CursorPosY = CursorPosY + CursorNewLine;
        display.setCursor(CursorPosX,CursorPosY);
        display.println("PRESS PLAY.");
        display.display();
        delay(500);
        CursorPosX = CursorPosXLeft;
        CursorPosY = CursorPosY + CursorNewLine;
        display.setCursor(CursorPosX,CursorPosY);
        display.println("LOADING SIDE B...");
        display.display();
        ModeTimeOutCheckReset();
      }

      if (ModeTimeOutCheck(1000)){ 
        ModeTimeOutCheckReset();
        TopLevelMode++;
        ModeTimeoutFirstTimeRun = true;
        Serial.println(">>> Leaving MODE_LOADING.");
      }
      break;
    }

    case MODE_RUN: {
      if (ModeTimeoutFirstTimeRun) {
        ModeTimeoutFirstTimeRun = false;
        Serial.println(">>> Entered MODE_RUN.");
        CursorPosX = CursorPosXLeft;
        CursorPosY = CursorPosY + CursorNewLine;
        display.setCursor(CursorPosX,CursorPosY);
        display.print(" (FWV ");
        display.print(FirmwareVersionMajor);
        display.print(".");
        display.print(FirmwareVersionMinor);
        display.print(".");
        display.print(FirmwareVersionPatch);
        display.print(")");
        display.display();
        CursorPosX = CursorPosXLeft;
        CursorPosY = CursorPosY + CursorNewLine + CursorNewLine;
        display.setCursor(CursorPosX,CursorPosY);
        display.println("READY.");
        display.display();
        delay(400);
        CursorPosX = CursorPosXLeft;
        CursorPosY = CursorPosY + CursorNewLine;
        display.setCursor(CursorPosX,CursorPosY);
        display.println("R");
        display.display();
        delay(KeyStrokeDelay);
        CursorPosX = CursorPosX + 6;
        display.setCursor(CursorPosX,CursorPosY);
        display.println("U");
        display.display();
        delay(KeyStrokeDelay);
        CursorPosX = CursorPosX + 6;
        display.setCursor(CursorPosX,CursorPosY);
        display.println("N");
        display.display();
        CursorPosX = CursorPosX + 6;
        ModeTimeOutCheckReset();
      }
      CursorBlink();
      if (ModeTimeOutCheck(500)){ 
        ModeTimeOutCheckReset();
        TopLevelMode++;
        CursorErase();
        ModeTimeoutFirstTimeRun = true;
        Serial.println(">>> Leaving MODE_RUN.");
      }
      break;
    }

    case MODE_SKETCH: {
      int16_t adc;
      uint16_t volt;
      if (ModeTimeoutFirstTimeRun) { 
        Serial.println(">>> Entered MODE_SKETCH.");
        OLEDBackgroundReset();
        ModeTimeoutFirstTimeRun = false;
      }
      
      // Arduino Analog Reading (Arduino with RP2040 allows 0-3.3V, full-scale reading with 10-bit resolution, 0-1023 )
      PotLeftADCCounts = analogRead(PIN_SAO_GPIO_1_ANA_POT_LEFT);
      PotRightADCCounts = analogRead(PIN_SAO_GPIO_2_ANA_POT_RIGHT);
      // Get analog readings of the two pots
      if (EASAnalogSource) {
        // Scale ADC counts to the useable screen with margins at end of pot travel.
        cursorX = map(PotLeftADCCounts , (1023-PotMarginAtLimit), PotMarginAtLimit, 0, 126);
        cursorY = map(PotRightADCCounts, PotMarginAtLimit, (1023-PotMarginAtLimit), 0, 126);
      }
      else {
        // Accelerometer Analog Reading (LIS3DH Analog reading is partial scale, limited between 0.9 and 1.8V)
        // Also scale these readings up to what Arduino ADC uses, so the rest of the processing code below doesn't need to change.
        adc = lis.readADC(1);
        // Limit reading to stay in bounds.
        if (adc < AccelADCRangeLowCounts ) { adc = AccelADCRangeLowCounts; }
        if (adc > AccelADCRangeHighCounts ) { adc = AccelADCRangeHighCounts; }
        // volt = map(adc, -32512, 32512, 1400, 900);
        volt = map(adc, AccelADCRangeLowCounts, AccelADCRangeHighCounts, AccelADCRangeHighmV, AccelADCRangeLowmV);
        #ifdef DEBUG_ADC
          Serial.print("ADC1-L:\t"); Serial.print(adc); 
          Serial.print(" ("); Serial.print(volt); Serial.print(" mV)  ");
        #endif
        // PotLeftADCCounts = map(adc, -32512, 32512, 1023, 0);
        cursorX = map(adc, AccelADCRangeLowCounts, AccelADCRangeHighCounts, 0, 126);
        adc = lis.readADC(2);
        // Limit reading to stay in bounds.
        if (adc < AccelADCRangeLowCounts ) { adc = AccelADCRangeLowCounts; }
        if (adc > AccelADCRangeHighCounts ) { adc = AccelADCRangeHighCounts; }
        // volt = map(adc, -32512, 32512, 1400, 900);
        volt = map(adc, AccelADCRangeLowCounts, AccelADCRangeHighCounts, AccelADCRangeHighmV, AccelADCRangeLowmV);
        #ifdef DEBUG_ADC
          Serial.print("ADC2-R:\t"); Serial.print(adc); 
          Serial.print(" ("); Serial.print(volt); Serial.print(" mV)  ");
        #endif
        // PotRightADCCounts = map(adc, -32512, 32512, 1023, 0);
        cursorY = map(adc, AccelADCRangeLowCounts, AccelADCRangeHighCounts, 126, 0);
      }
      adc = lis.readADC(3);
      volt = map(adc, AccelADCRangeLowCounts, AccelADCRangeHighCounts, AccelADCRangeHighmV, AccelADCRangeLowmV);
      #ifdef DEBUG_ADC
        Serial.print("ADC3-?:\t"); Serial.print(adc); 
        Serial.print(" ("); Serial.print(volt); Serial.print(" mV)  ");
        Serial.println();
      #endif

      // Glitch rejection
      if (cursorX > 130) { cursorX = 0;}
      if (cursorY > 130) { cursorY = 0;}

      // Hysteresis
      // if (cursorX > (cursorXold + CursorHystersisLimit) ) { cursorX = cursorXold;}
      // if (cursorX < (cursorXold - CursorHystersisLimit) ) { cursorX = cursorXold;}

      // Filtering
      #ifdef EMA_FILTER
        double inputX = (double)cursorX;
        double outputX = emaFilterX.Run(inputX);
        cursorX = (uint16_t)outputX;
      #endif
      #ifdef IIR_FILTER
        cursorX = IIRFilterX.Run(cursorX);
      #endif

      #ifdef EMA_FILTER
        double inputY = (double)cursorY;
        double outputY = emaFilterY.Run(inputY);
        cursorY = (uint16_t)outputY;
      #endif
      #ifdef IIR_FILTER
        cursorY = IIRFilterY.Run(cursorY);
      #endif


      PotLeftADCCountsOld = PotLeftADCCounts;
      PotRightADCCountsOld = PotRightADCCounts;
      cursorXold = cursorX;
      cursorYold = cursorY;
      #ifdef DEBUG_CURSOR
        Serial.print("Cursor position: ");
        Serial.print(cursorX);
        Serial.print(",");
        Serial.println(cursorY);
      #endif
      // Update the display
      if (EASBackground) { display.drawRect(cursorX, cursorY, 2, 2, OLED_BLACK); }
      else { display.drawRect(cursorX, cursorY, 2, 2, OLED_WHITE); }
      display.display();

      // Check for gestures
      if (AccelerometerSenseGestureErase()) { 
        OLEDBackgroundReset(); 
        }
      /* Disable these modes in V1.3.1
      if (AccelerometerSenseGestureChangeBackground()) {
        if (EASBackground) { 
          EASBackground = 0;
          OLEDBackgroundReset();
          }
        else {
          EASBackground = 1;
          OLEDBackgroundReset();
          }
        }
      if (AccelerometerSenseGestureChangeADCSource()) {
        if (EASAnalogSource) { EASAnalogSource = 0;  }
        else                 { EASAnalogSource = 1; }
        }
      */
      break;
    }

    case MODE_CALIBRATE: {
      static int16_t CalAccelBuffer = 800; // The readings are noisey, this buffer value keeps the min/max away from the edge.
      static int16_t CalAccelADC1maxCounts = 0;
      static int16_t CalAccelADC1avgCounts = 0;
      static int16_t CalAccelADC1minCounts = 0;
      static int16_t CalAccelADC2maxCounts = 0;
      static int16_t CalAccelADC2avgCounts = 0;
      static int16_t CalAccelADC2minCounts = 0;
      static int16_t CalAccelADCmaxUpperLimCounts = 0;
      static int16_t CalAccelADCmaxLowerLimCounts = 0;
      static int16_t CalAccelADCminUpperLimCounts = 0;
      static int16_t CalAccelADCminLowerLimCounts = 0;
      uint8_t CursorPosXforX;
      uint8_t CursorPosYforX;
      uint8_t CursorPosXforY;
      uint8_t CursorPosYforY;
      if (ModeTimeoutFirstTimeRun) {
        ModeTimeoutFirstTimeRun = false;
        Serial.println(">>> Entered MODE_RUN.");
        OLEDClear();
        ModeTimeOutCheckReset();
      }
      // Check ADC values
      int16_t adc1 = lis.readADC(1);
      double inputX = (double)adc1;
      double outputX = emaFilterX.Run(inputX);
      CalAccelADC1avgCounts = (int16_t)outputX;
      if((CalAccelADC1avgCounts - CalAccelBuffer) > CalAccelADC1maxCounts) {CalAccelADC1maxCounts = CalAccelADC1avgCounts - CalAccelBuffer;}
      if((CalAccelADC1avgCounts + CalAccelBuffer) < CalAccelADC1minCounts) {CalAccelADC1minCounts = CalAccelADC1avgCounts + CalAccelBuffer;}

      int16_t adc2 = lis.readADC(2);
      double inputY = (double)adc2;
      double outputY = emaFilterX.Run(inputY);
      CalAccelADC2avgCounts = (int16_t)outputY;
      if((CalAccelADC2avgCounts - CalAccelBuffer) > CalAccelADC2maxCounts) {CalAccelADC2maxCounts = CalAccelADC2avgCounts - CalAccelBuffer;}
      if((CalAccelADC2avgCounts + CalAccelBuffer) < CalAccelADC2minCounts) {CalAccelADC2minCounts = CalAccelADC2avgCounts + CalAccelBuffer;}

      if (CalAccelADC1maxCounts < CalAccelADC2maxCounts) {AccelADCRangeHighCounts = CalAccelADC1maxCounts; }
      else { AccelADCRangeHighCounts = CalAccelADC2maxCounts; }
      if (CalAccelADC1minCounts < CalAccelADC2minCounts) {AccelADCRangeLowCounts = CalAccelADC2minCounts; }
      else { AccelADCRangeLowCounts = CalAccelADC1minCounts; }

      // Update the display
      uint8_t DataOffset = 68;
      display.clearDisplay();
      display.setCursor(2,0);
      display.print("FWV: ");
      display.print(FirmwareVersionMajor);
      display.print(".");
      display.print(FirmwareVersionMinor);
      display.print(".");
      display.print(FirmwareVersionPatch);
      display.setCursor(2,8);
      display.println("Turn both knobs full");
      display.setCursor(2,16);
      display.println("left and full right.");
      display.setCursor(2,24);
      display.println("L MAX (X):");
      display.setCursor(2,32);
      display.println("L NOW (X):");
      display.setCursor(2,40);
      display.println("L MIN (X):");
      display.setCursor(2,48);
      display.println("R MAX (Y):");
      display.setCursor(2,56);
      display.println("R NOW (Y):");
      display.setCursor(2,64);
      display.println("R MIN (Y):");

      display.setCursor(DataOffset,24);
      display.println(CalAccelADC1maxCounts);
      display.setCursor(DataOffset,32);
      display.println(adc1);
      display.setCursor(DataOffset,40);
      display.println(CalAccelADC1minCounts);
      display.setCursor(DataOffset,48);
      display.println(CalAccelADC2maxCounts);
      display.setCursor(DataOffset,56);
      display.println(adc2);
      display.setCursor(DataOffset,64);
      display.println(CalAccelADC2minCounts);
      display.display();

      // Check for timeout from this mode
      if (ModeTimeOutCheck(6000)){ 
        ModeTimeOutCheckReset();
        TopLevelMode = MODE_SKETCH;
        ModeTimeoutFirstTimeRun = true;
        Serial.println(">>> Timeout. Leaving MODE_CALIBRATE.");
      }
      break;
    }

    case MODE_AT_THE_END_OF_TIME: {
      Serial.println(">>> Stuck in the MODE_AT_THE_END_OF_TIME! <<<");
      break;
    }

    default: {
      Serial.println(">>> Something is broken! <<<");
      break;
    }
  }
    
  if(!digitalRead(UserButtonPin1)) {
    TopLevelMode = MODE_CALIBRATE;
  }

}
